mirage335/ArduinoDAQ/hacdcCNC/USB_DAQ/outp0_original_back.png

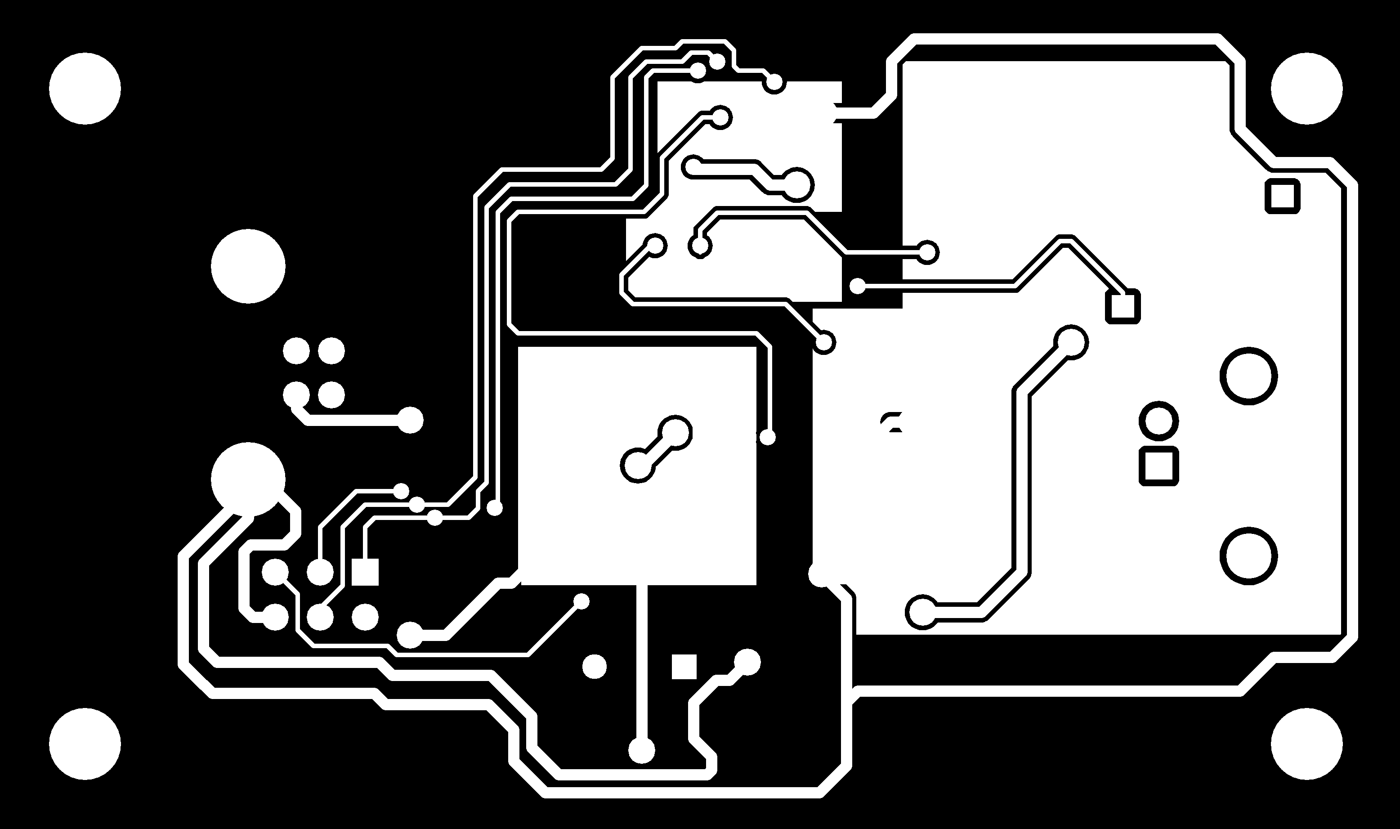
hacdcCNC/USB_DAQ/outp0_original_back.png
