mirage335/ArduinoDAQ/hacdcCNC/USB_DAQ/outp1_original_front.png

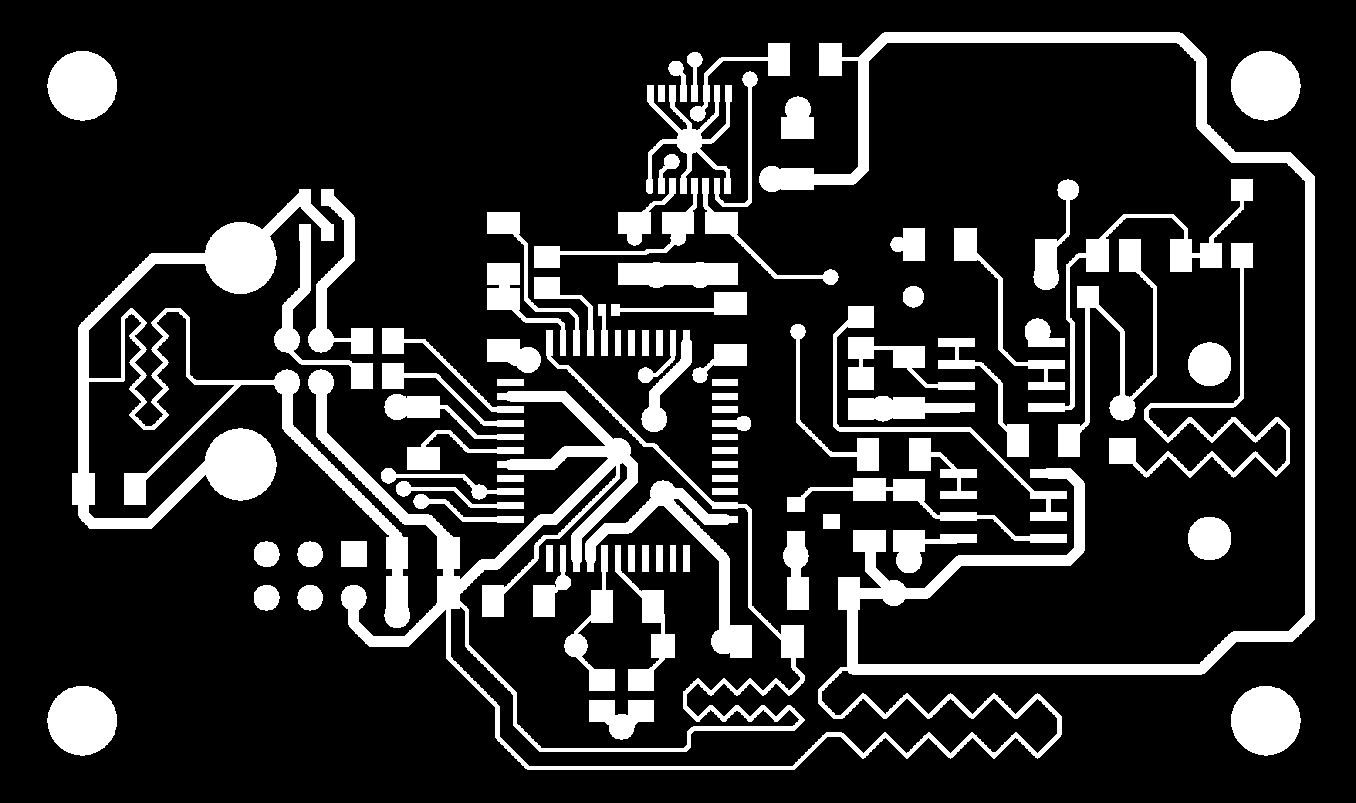
hacdcCNC/USB_DAQ/outp1_original_front.png
