mirage335/ArduinoDAQ/hacdcCNC/USB_DAQ/outp3_outline_filled.png

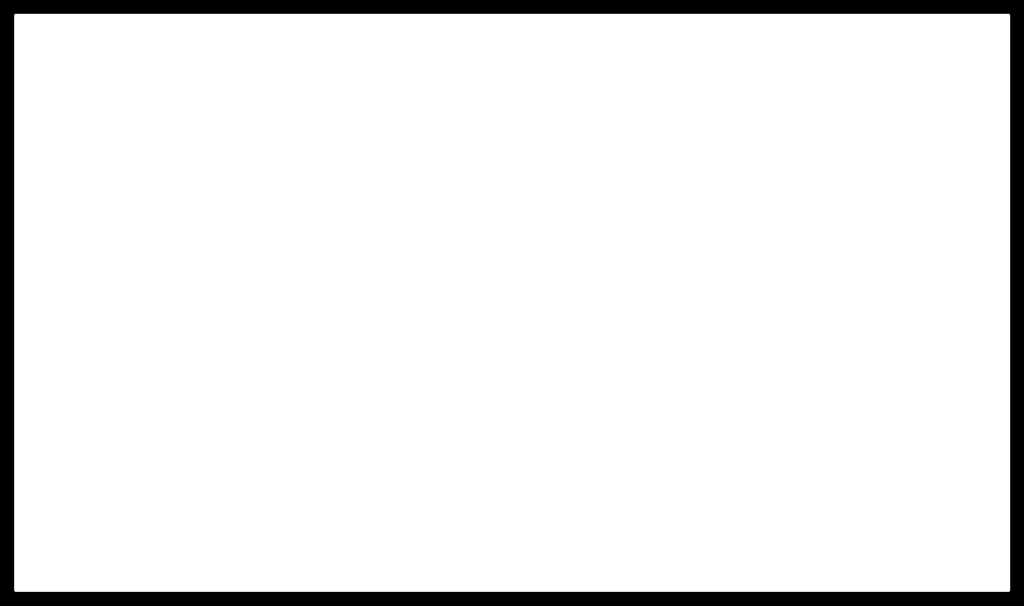
hacdcCNC/USB_DAQ/outp3_outline_filled.png
