mirage335/ArduinoDAQ/hacdcCNC/USB_DAQ/outp6_traced.png

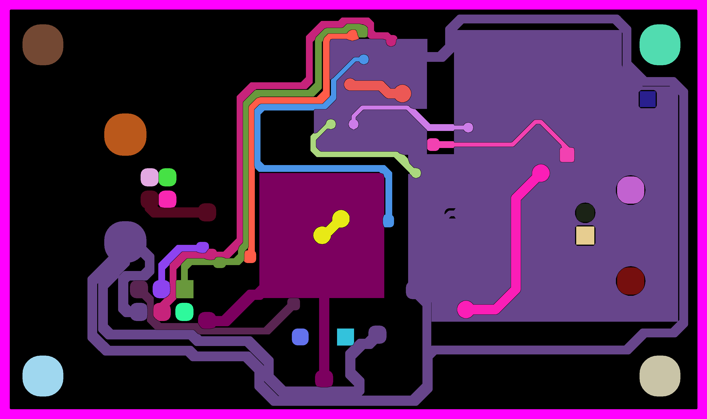
hacdcCNC/USB_DAQ/outp6_traced.png
